mrheltic/Bilancia-SaT/Test/Post_Calibration_Test/Results/hysteresis.csv

Known weight | Measured weight
10 | 13
20 | 10
50 | 24
100 | 0
200 | 56
200 | 59
100 | 133
50 | 131
20 | 96
10 | 53
