mrheltic/Bilancia-SaT/Test/Repeatability/Results/repeatability.csv

Measures
20.03
19.99
20.04
20
20.04
