mrheltic/Bilancia-SaT/Latex document/medias/test/post/hysteresis_results.jpg

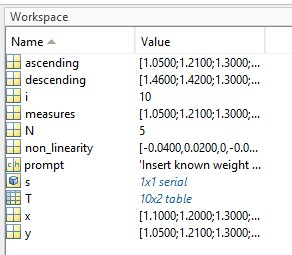
Latex document/medias/test/post/hysteresis_results.jpg
